taylorconor/threeboard/documentation/images/hardware/usb/connector_type_c.png

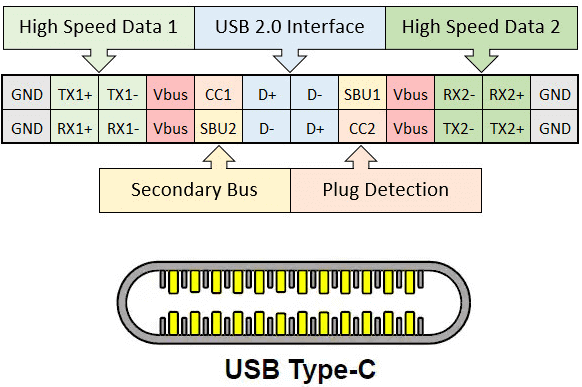
documentation/images/hardware/usb/connector_type_c.png
