taylorconor/threeboard/firmware/simulator/simulator.h

#pragma once

#include <atomic>
#include <fstream>
#include <functional>
#include <thread>

#include "simulator/components/i2c_eeprom.h"
#include "simulator/components/uart.h"
#include "simulator/components/usb_host_impl.h"
#include "simulator/simavr/simavr.h"
#include "simulator/simulator_delegate.h"
#include "simulator/simulator_state.h"
#include "simulator/ui/ui_delegate.h"
#include "simulator/util/state_storage.h"
#include "src/keypress.h"

namespace threeboard {
namespace simulator {

// This class provides an interface on top of the simavr instance to enable it
// to be integrated into the simulator binary and in tests.
class Simulator : public SimulatorDelegate {
 public:
  Simulator(Simavr *simavr, StateStorage *state_storage);
  virtual ~Simulator();

  void RunAsync();
  void Reset();

  DeviceState GetDeviceState();
  SimulatorState GetSimulatorState() const;
  void HandleKeypress(char key, bool state);
  void HandleKeypress(const Keypress &keypress, bool state);
  void WaitForUsbOutput(const std::chrono::milliseconds &timeout);

  uint64_t GetCurrentCpuCycle() const;
  void ToggleGdb(uint16_t port) const;
  void EnableLogging(UIDelegate *ui_delegate);
  std::string GetLogFile() const;

 private:
  void HandleUsbOutput(uint8_t mod_code, uint8_t key_code) override;
  void HandlePortWrite(uint8_t port, uint8_t value);
  void UpdateLedState(uint8_t row);

  void InternalRunAsync();

  Simavr *simavr_;
  std::unique_ptr<Uart> uart_;
  std::thread sim_thread_;
  std::atomic<bool> is_running_;
  std::atomic<bool> should_reset_;
  UsbHostImpl usb_host_;
  I2cEeprom eeprom0_;
  DeviceState device_state_;
  std::string log_file_path_;
  std::ofstream log_stream_;
  std::chrono::system_clock::time_point last_usb_output_;

  std::unique_ptr<PortWriteCallback> portb_write_callback_;
  std::unique_ptr<PortWriteCallback> portd_write_callback_;
};

}  // namespace simulator
}  // namespace threeboard
