taylorconor/threeboard/firmware/simulator/sim_ui.h

#pragma once

#include <atomic>
#include <functional>
#include <thread>
#include <unordered_map>

namespace threeboard {
namespace simulator {

// This class is responsible for rendering the simulator UI to the terminal. It
// has no knowledge of the simulator's existence, it relies on its owner setting
// the relevant simulator fields via the setter methods. A callback can be
// provided (StateUpdateCallback) which is called before each render frame, to
// allow the owner to set the current state of the simulator in the UI.
class SimUI {
public:
  enum class Key {
    KEY_A, // 'X' key on threeboard.
    KEY_S, // 'Y' key on threeboard.
    KEY_D, // 'Z' key on threeboard.
    KEY_Q, // 'Q' for quit.
  };

  using StateUpdateCallback = std::function<void()>;
  using KeypressCallback = std::function<void(Key, bool)>;

  SimUI(const StateUpdateCallback &, const KeypressCallback &, const int &,
        const uint64_t &);
  ~SimUI();

  void StartRenderLoopAsync();
  void ClearLedState();

  void SetR(bool);
  void SetG(bool);
  void SetB(bool);
  void SetProg(bool);
  void SetErr(bool);
  void SetStatus(bool);
  void SetBank0(bool, uint8_t);
  void SetBank1(bool, uint8_t);

private:
  void UpdateKeyState();
  void RenderLoop();
  void DrawLeds();
  void DrawKeys();
  void DrawStatusText();
  std::string GetClockSpeedString();
  std::string GetCpuStateBreakdownString();

  StateUpdateCallback state_update_callback_;
  KeypressCallback keypress_callback_;

  // Reference variables to frequently-updated properties of the simulator.
  const int &sim_state_;
  const uint64_t &sim_cycle_;

  // Keep track of the simulator cycle count from the previous render pass so we
  // can calculate CPU frequency.
  uint64_t prev_sim_cycle_;

  // Memoize some stats so we don't have to constantly recalculate and so that
  // their values don't update so fast they flicker.
  uint8_t cycles_since_memo_update_;
  std::string freq_str_memo_ = "Loading...";
  std::string state_str_memo_ = "Loading...";

  std::unordered_map<uint8_t, uint64_t> cpu_mode_distribution_;

  uint8_t key_a_ = 0;
  uint8_t key_s_ = 0;
  uint8_t key_d_ = 0;

  std::atomic<bool> is_running_;
  uint64_t current_frame_ = 0;

  uint8_t r_ = 0;
  uint8_t g_ = 0;
  uint8_t b_ = 0;
  uint8_t prog_ = 0;
  uint8_t err_ = 0;
  uint8_t status_ = 0;
  uint8_t bank0_[8] = {};
  uint8_t bank1_[8] = {};
  std::unique_ptr<std::thread> render_thread_;
};
} // namespace simulator
} // namespace threeboard
